mhorimoto/k2503100/DOCS/DOC190227-20190227140005.pdf

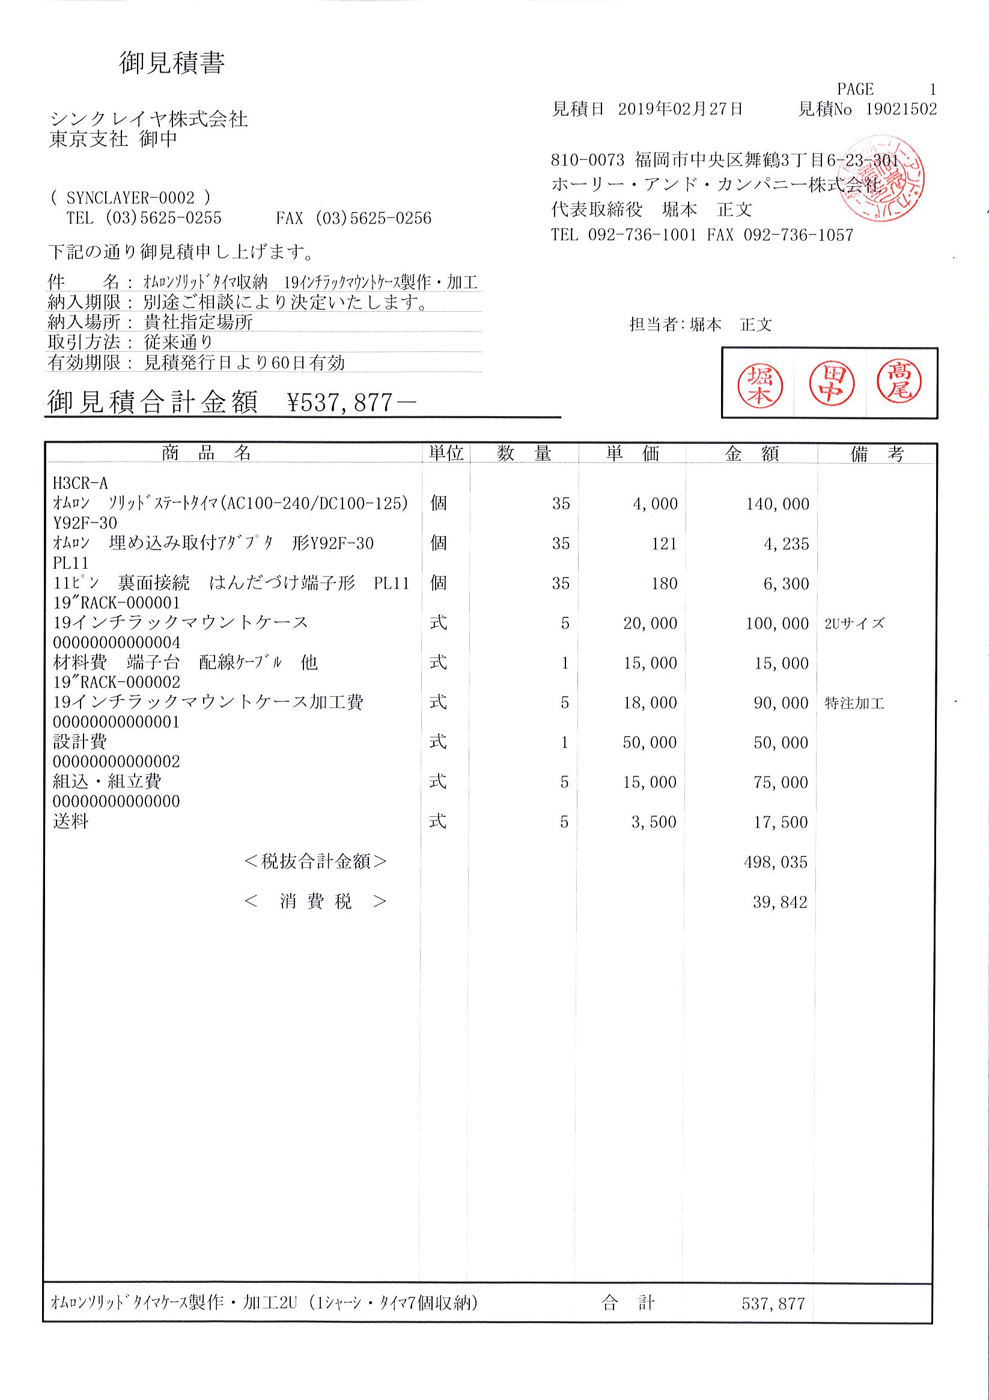
[picture p5: page 1]
