mhorimoto/k2503100/DOCS/image-sketch-1st.pdf

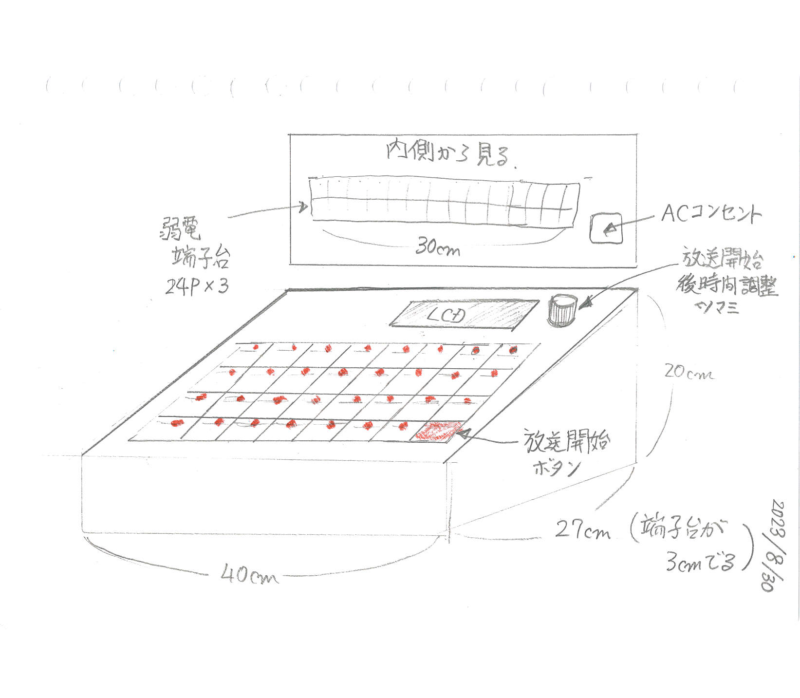
[picture p6: page 1]
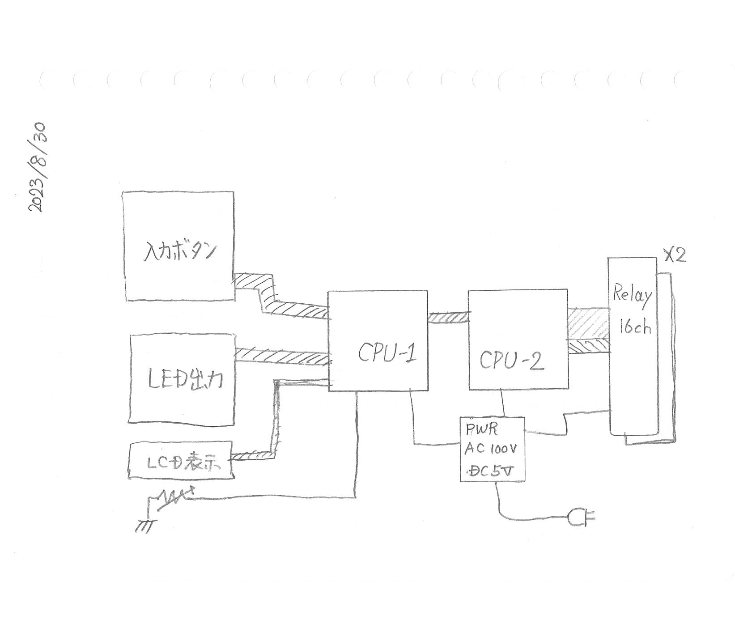
[picture p7: page 2]
