mhorimoto/k2503100/DOCS/workarea/Proforma  Invoice -PCBgogo20250206165503.pdf

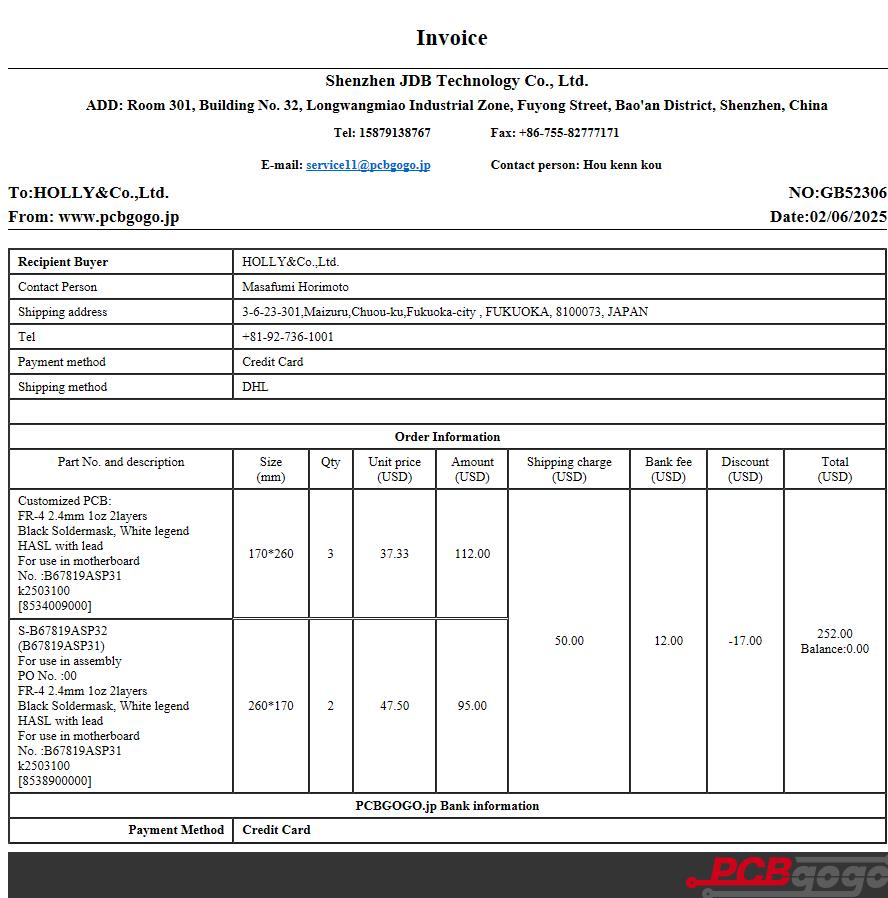
[picture p8: page 1]
