mhorimoto/k2503100/DOCS/workarea/20250203-case外観設計.pdf

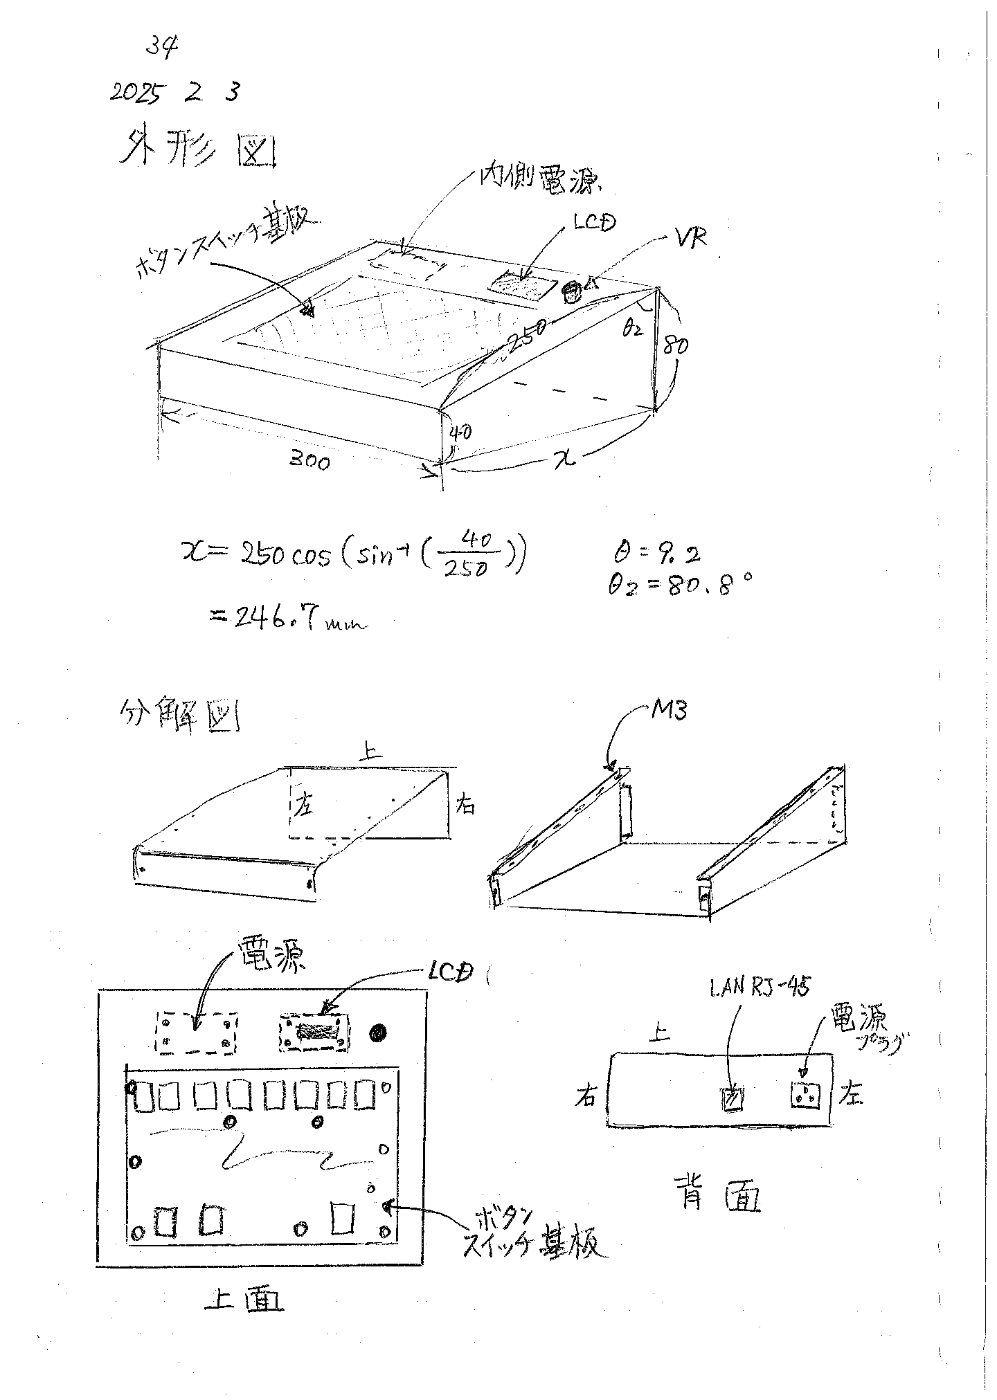
[picture p9: page 1]
