mhorimoto/k2503100/DOCS/workarea/PWR-LCD.pdf

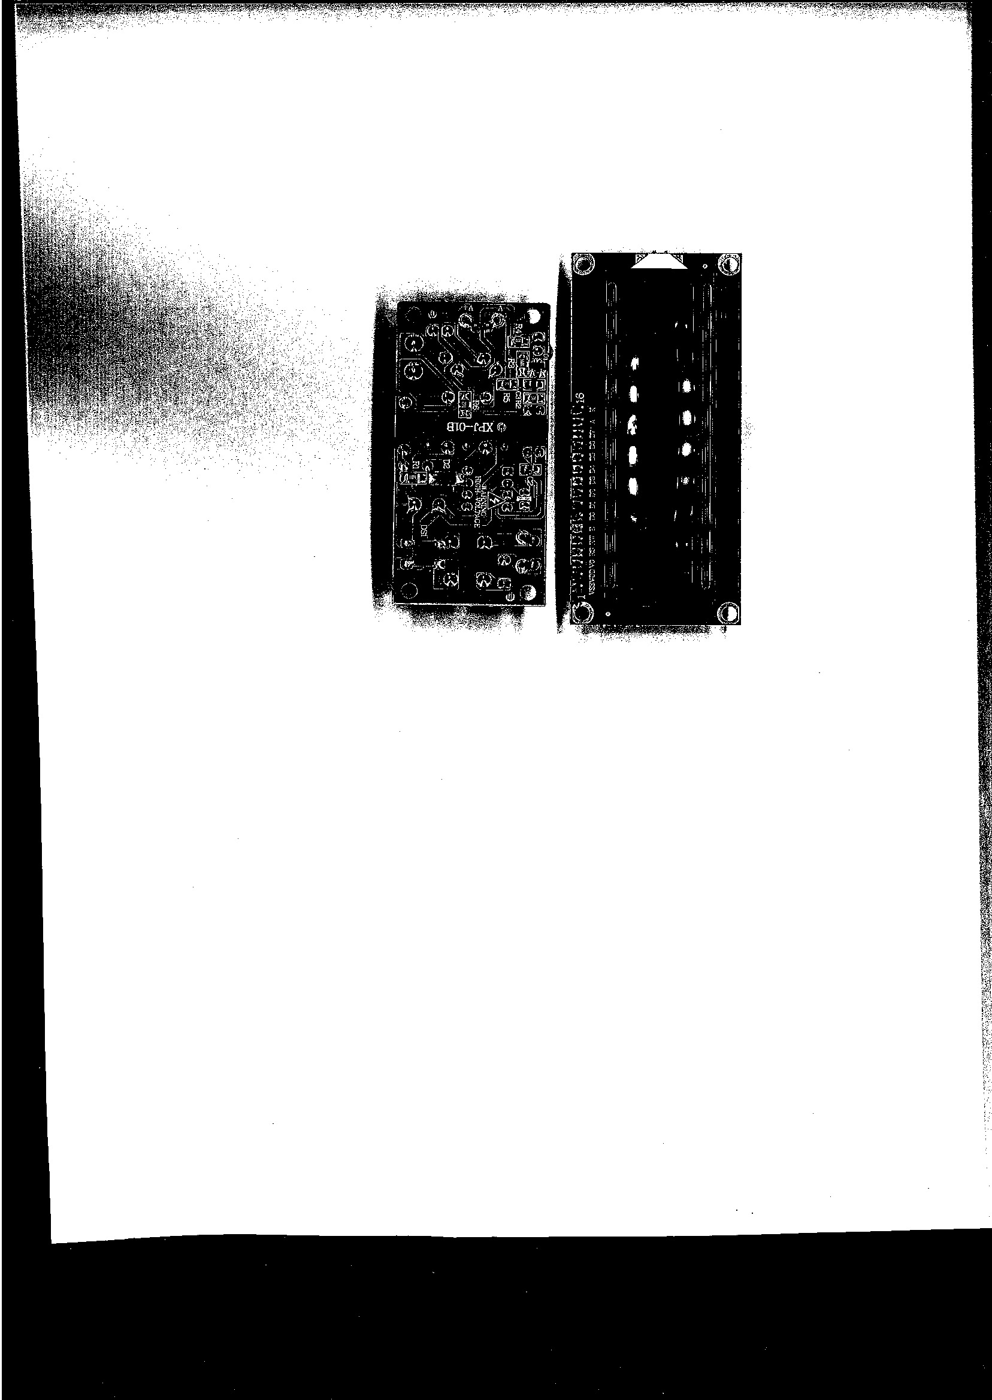
[picture p10: page 1]
