mhorimoto/k2503100/DOCS/workarea/S-B67819ASP32サンプル写真確認/2.jpg

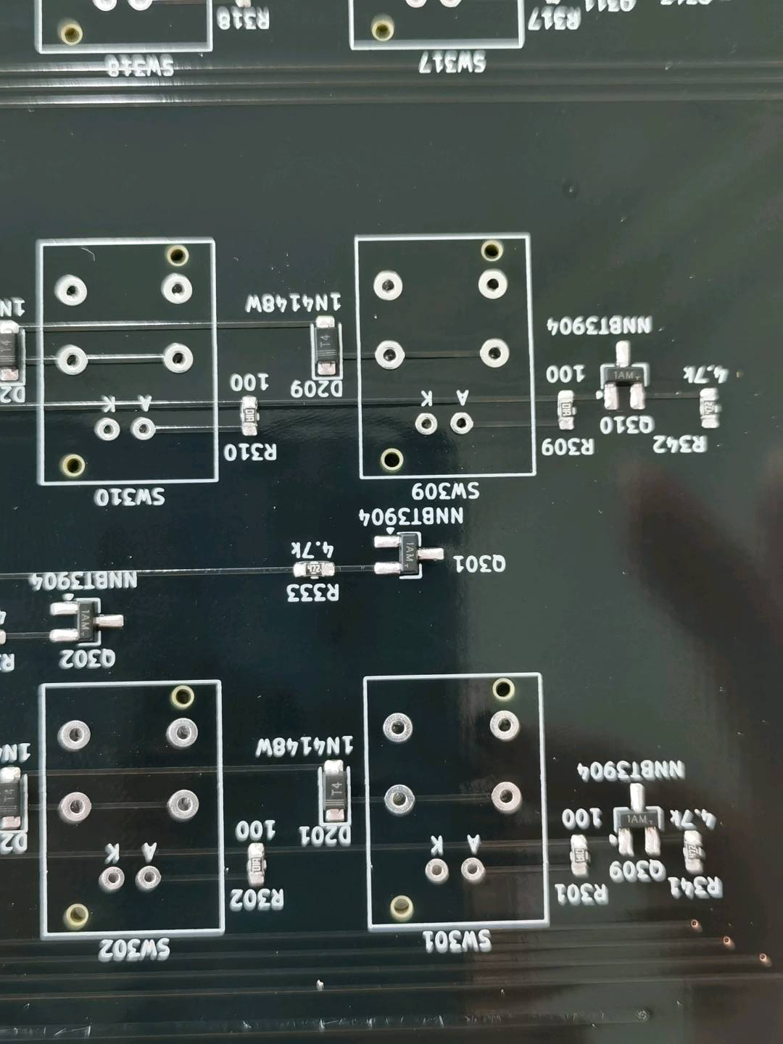
DOCS/workarea/S-B67819ASP32サンプル写真確認/2.jpg
