mhorimoto/k2503100/DOCS/image-sketch-2nd.pdf

## FM告知接点 (屋外のみ)

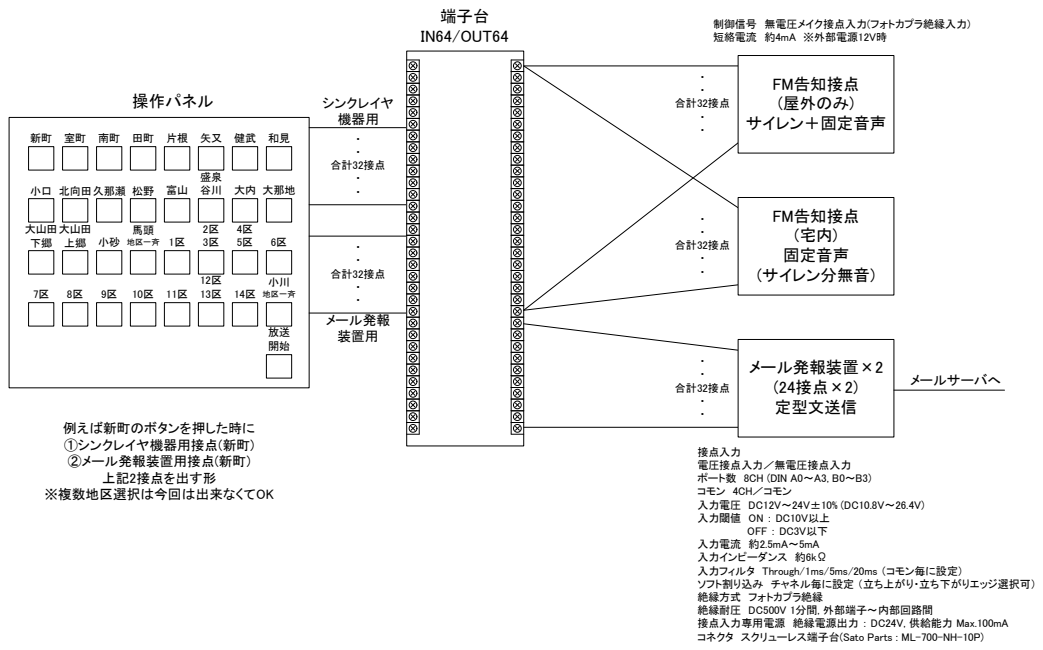
[picture p14: page 1]
サイレン＋固定音声; FM告知接点 (宅内) 固定音声 (サイレン分無音); メール発報装置×2 (24接点×2) 定型文送信; 操作パネル; シンクレイヤ; 機器用; メール発報 装置用; 端子台 IN64/OUT64; 大山田 下郷; 大山田; メールサーバへ; 地区一斉; OFF ： DC3V以下; 例えば新町のボタンを押した時に ①シンクレイヤ機器用接点(新町) ②メール発報装置用接点(新町) 上記2接点を出す形 ※複数地区選択は今回は出来なくてOK

制御信号　無電圧メイク接点入力(フォトカプラ絶縁入力)
短絡電流　約4mA　※外部電源12V時

谷川 大内 大那地

小口 北向田久那瀬 松野 富山

接点入力
電圧接点入力／無電圧接点入力
ポート数　8CH (DIN A0～A3, B0～B3)
コモン　4CH／コモン
入力電圧　DC12V～24V±10% (DC10.8V～26.4V)
入力閾値　ON ： DC10V以上
入力電流　約2.5mA～5mA
入力インピーダンス　約6kΩ
入力フィルタ　Through/1ms/5ms/20ms （コモン毎に設定）
ソフト割り込み　チャネル毎に設定 （立ち上がり・立ち下がりエッジ選択可）
絶縁方式　フォトカプラ絶縁
絶縁耐圧　DC500V 1分間, 外部端子～内部回路間
接点入力専用電源　絶縁電源出力 ： DC24V, 供給能力 Max.100mA
コネクタ　スクリューレス端子台(Sato Parts : ML-700-NH-10P)
