mhorimoto/k2503100/KiCAD/schema.pdf

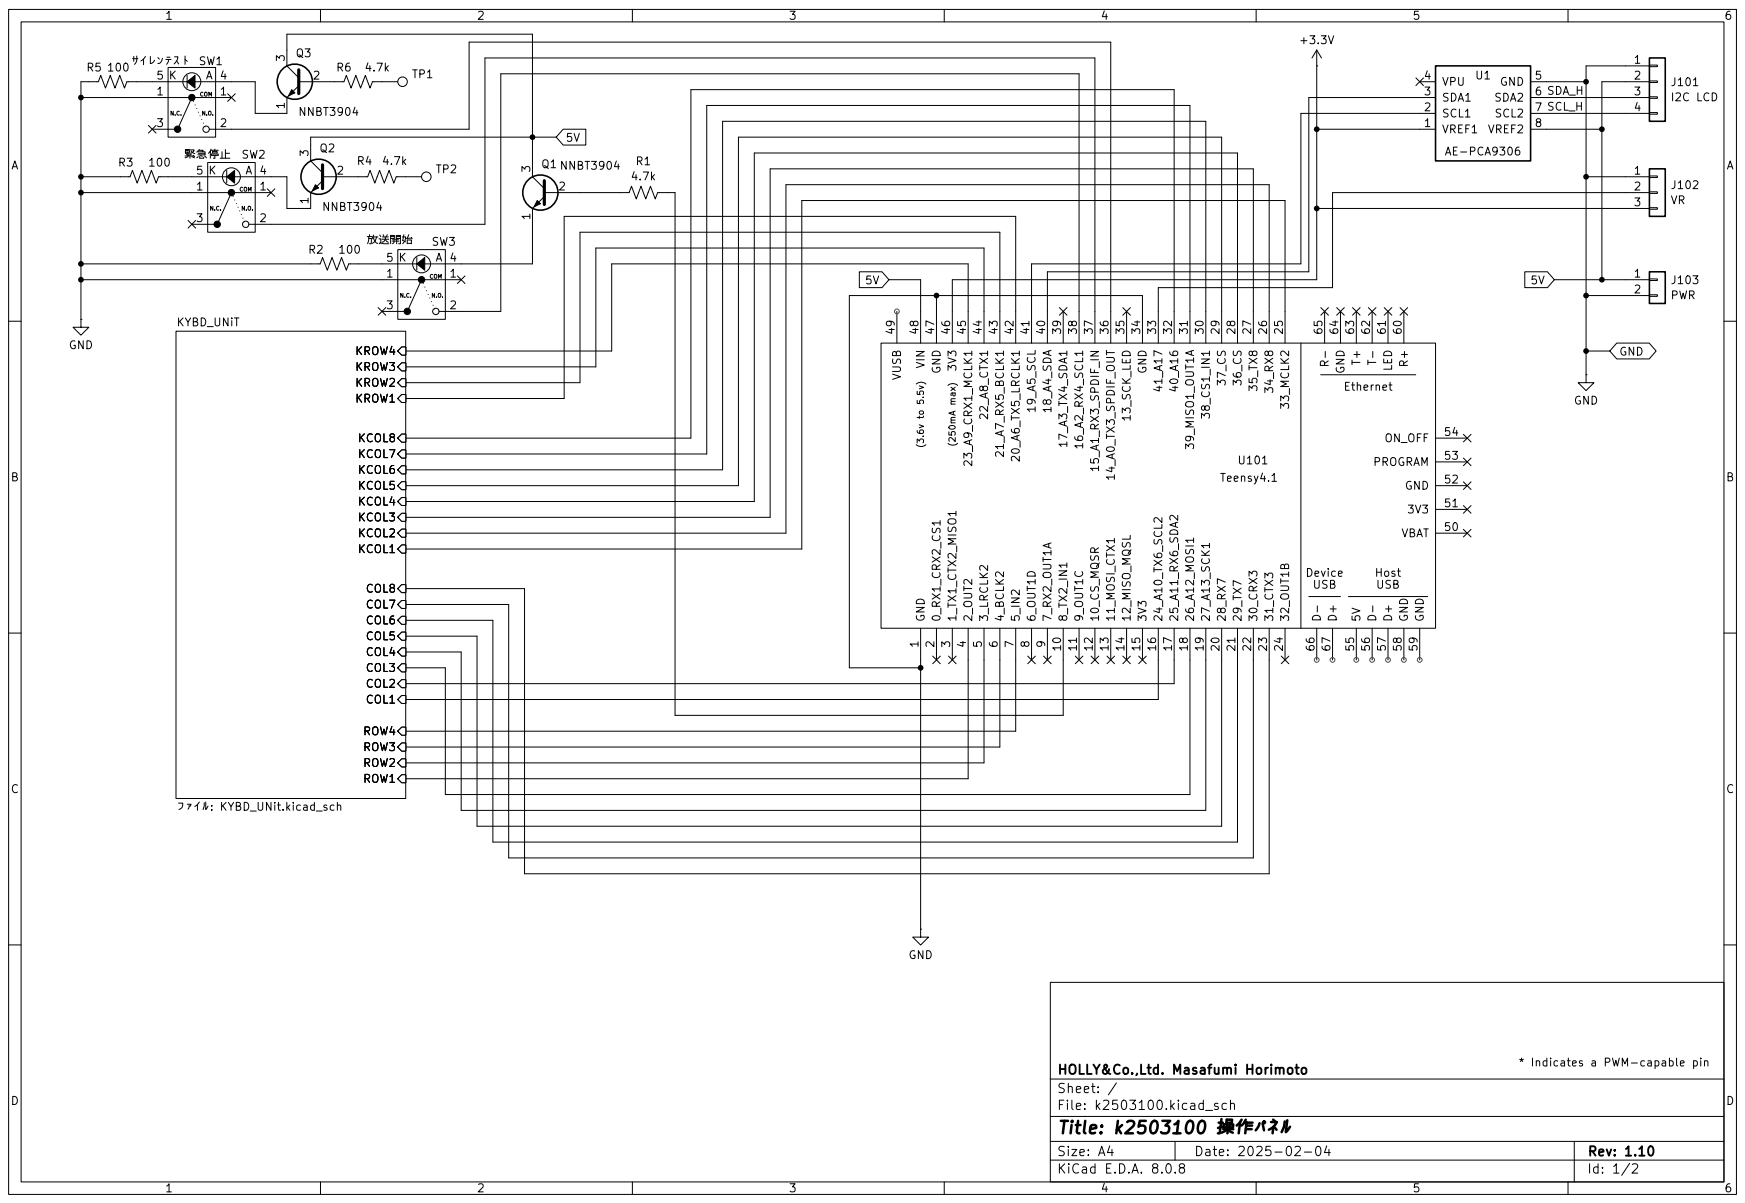
[picture p21: page 1]

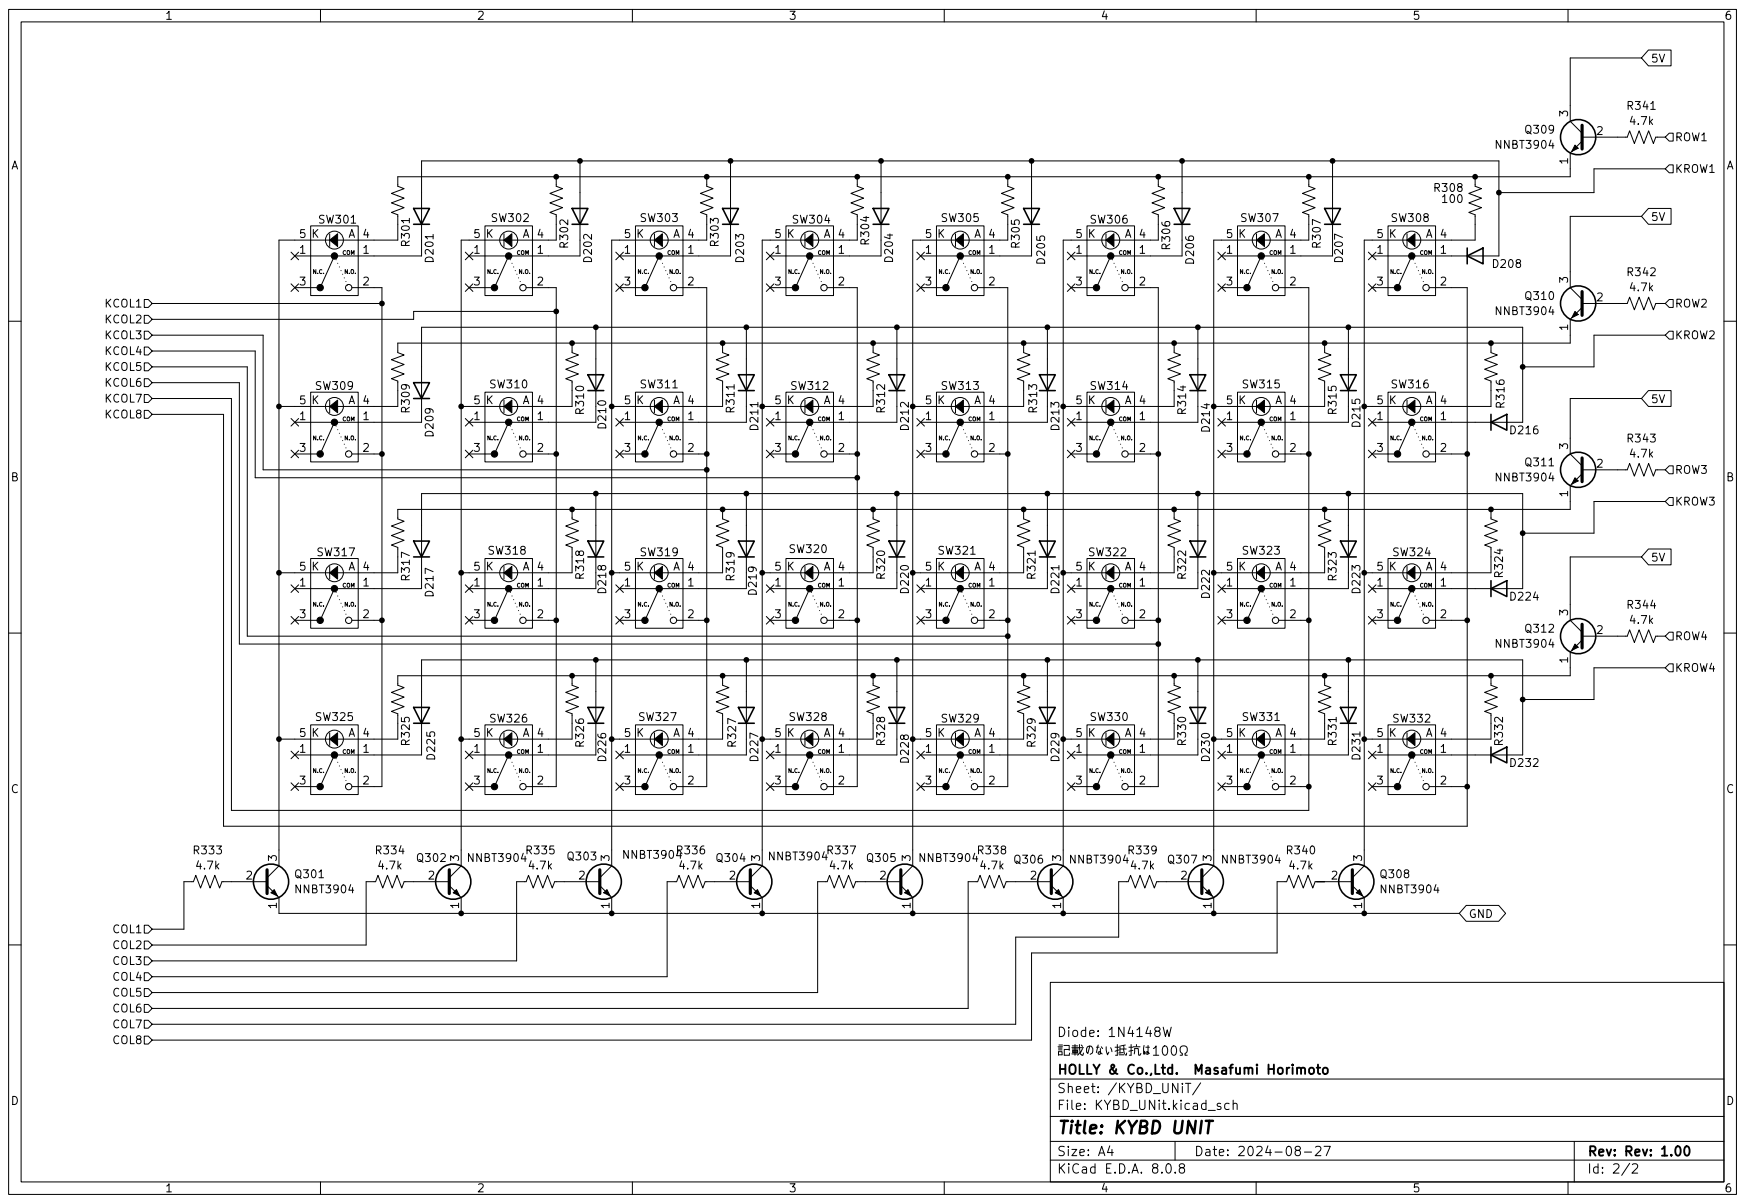
[picture p22: page 2]
