mhorimoto/k2503100/KiCAD/case1.pdf

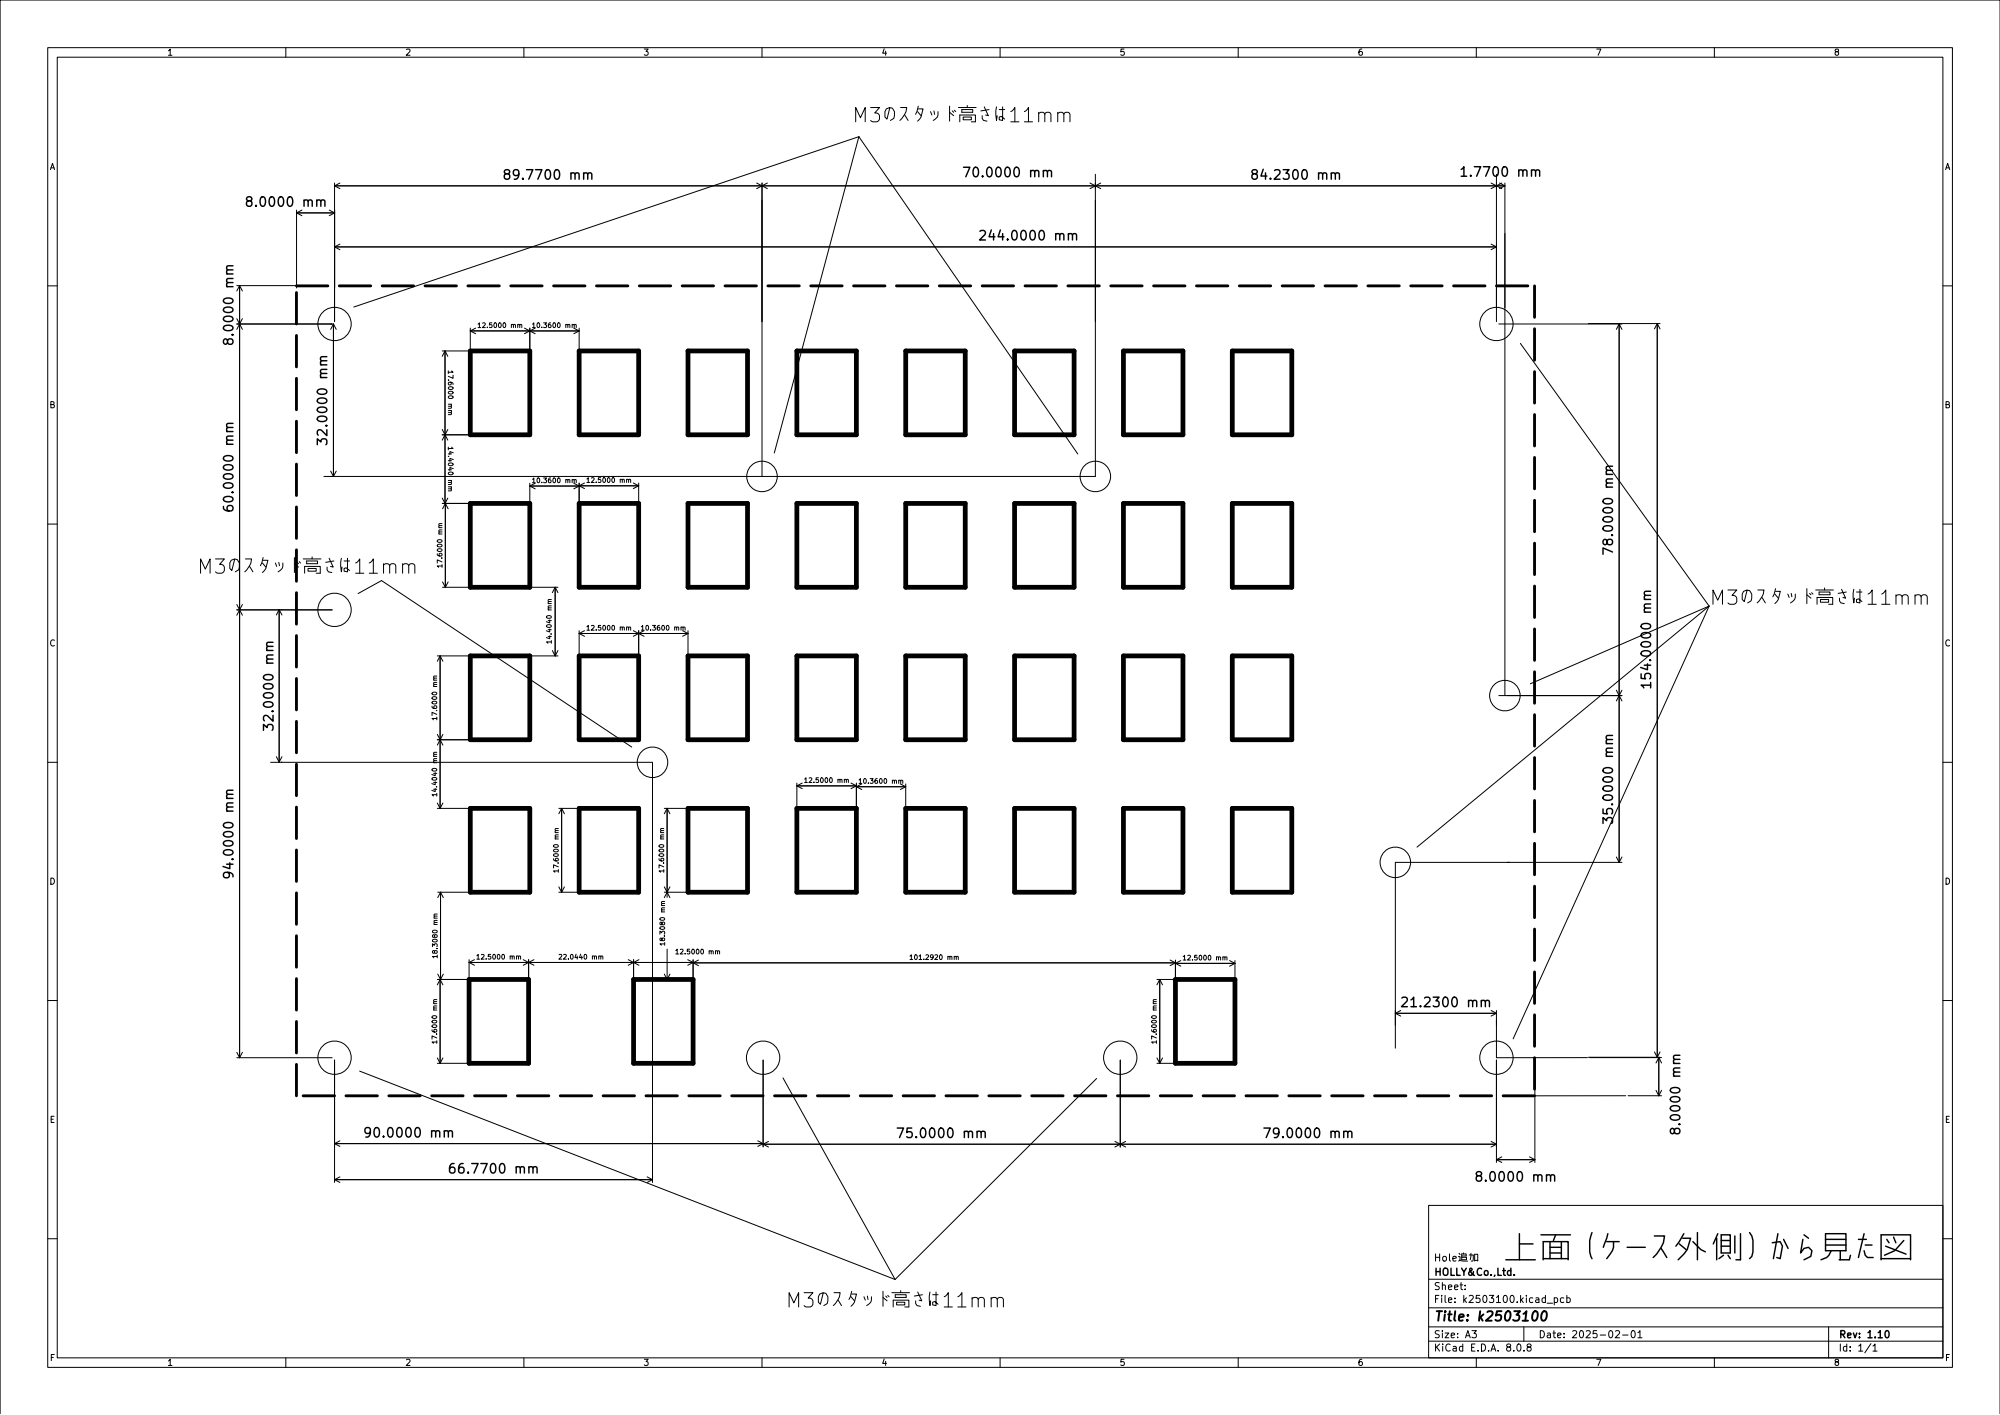
[picture p23: page 1]
