mhorimoto/k2503100/DOCS/workarea/W21888A0000.pdf

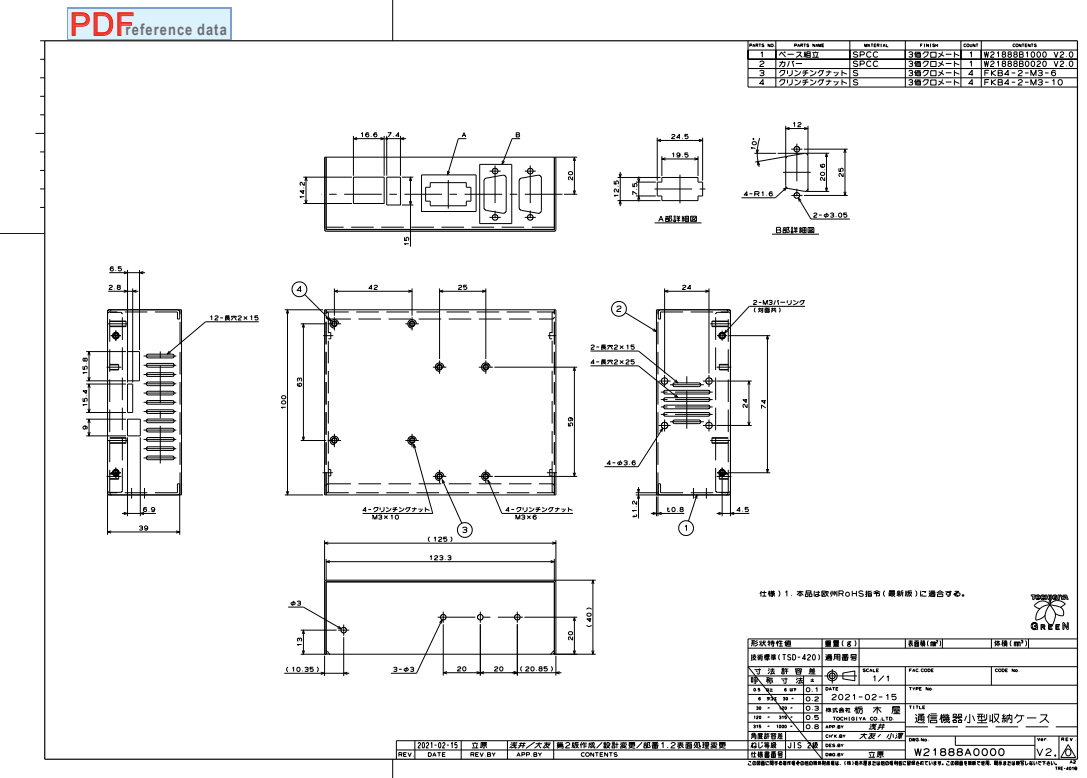
[picture p24: page 1]
PDFreference data
