mhorimoto/k2503100/DOCS/workarea/W21935A0000.pdf

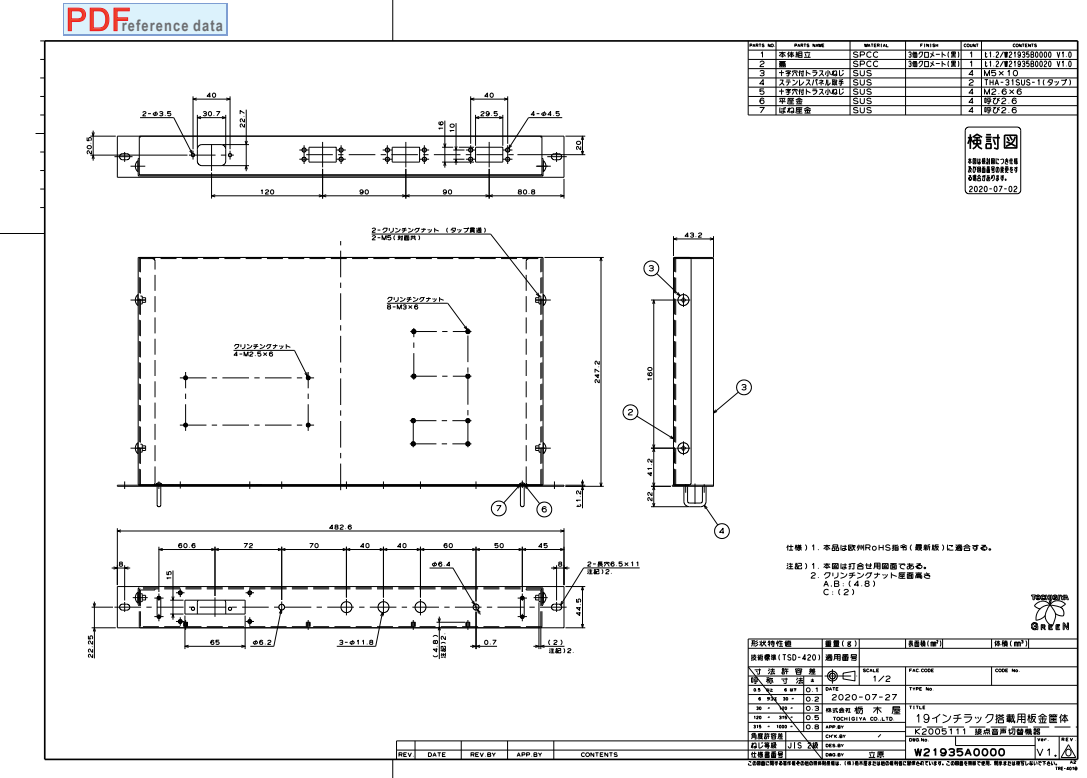
[picture p25: page 1]
PDFreference data

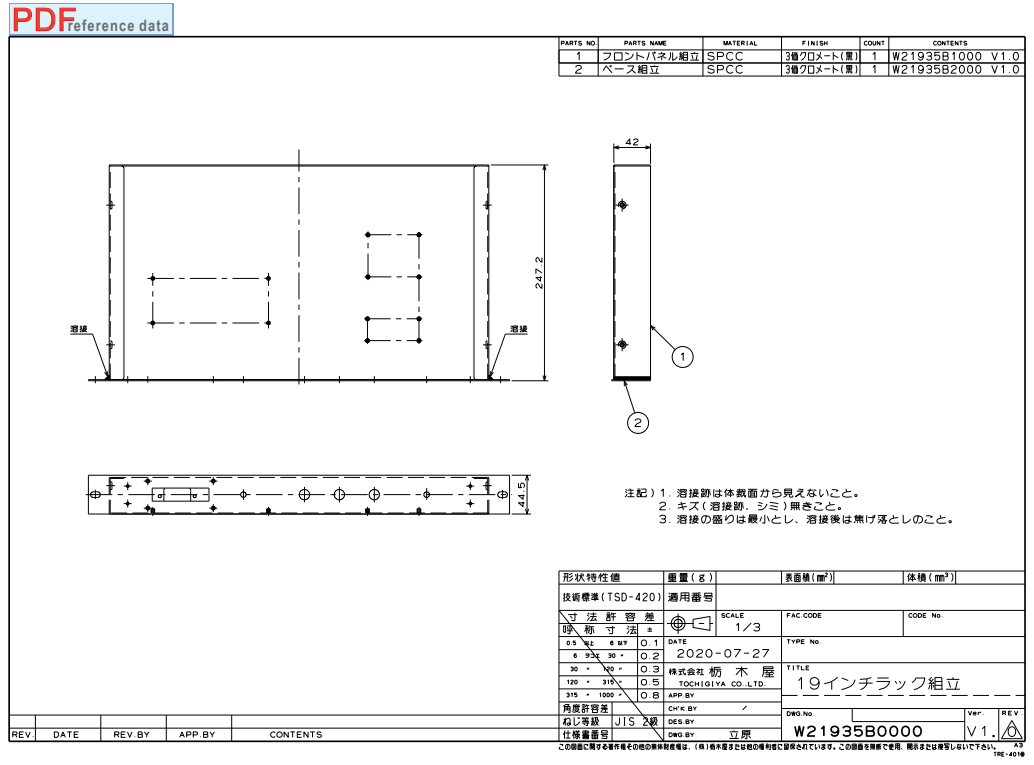
[picture p26: page 2]

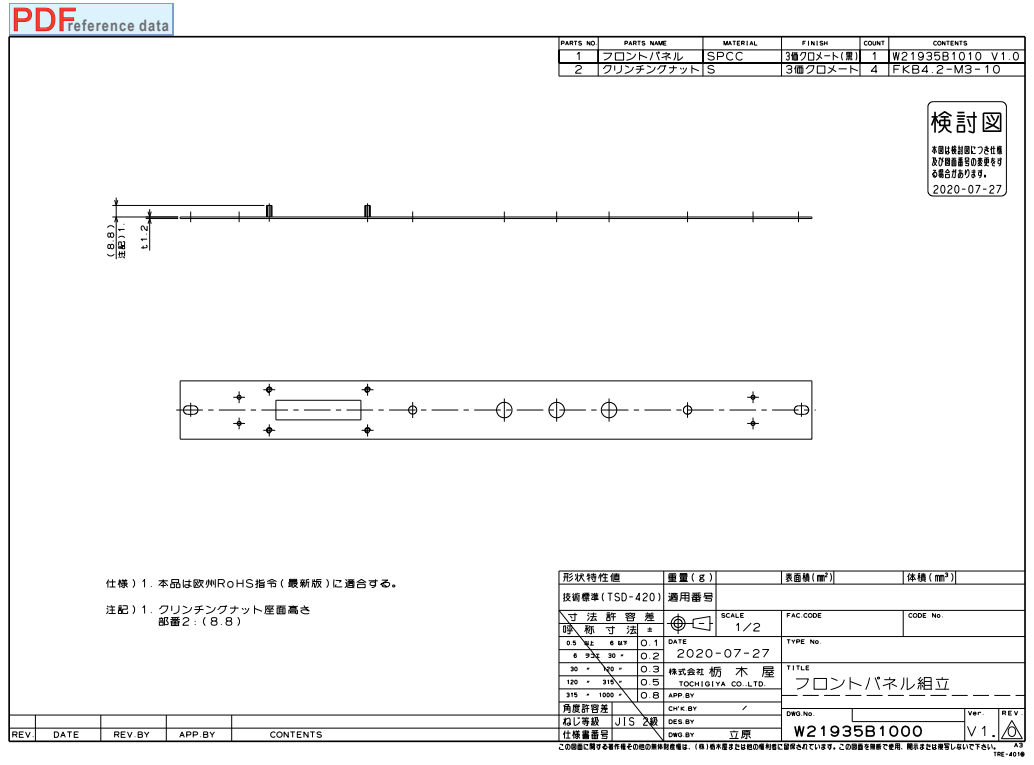
[picture p27: page 3]

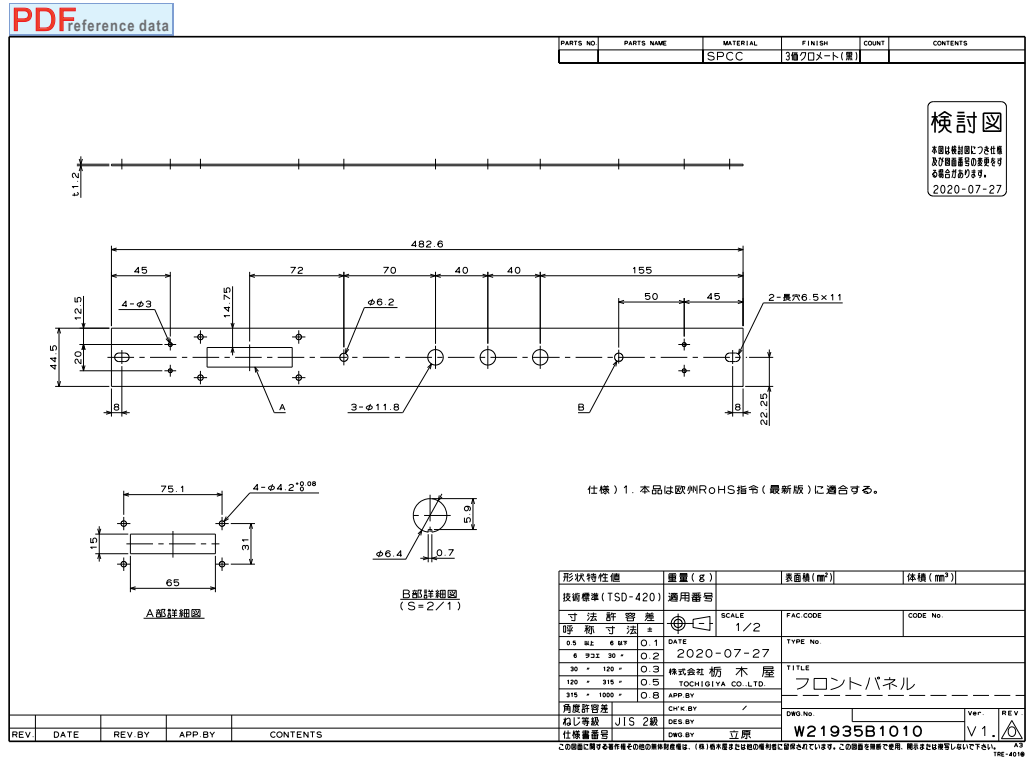
[picture p28: page 4]

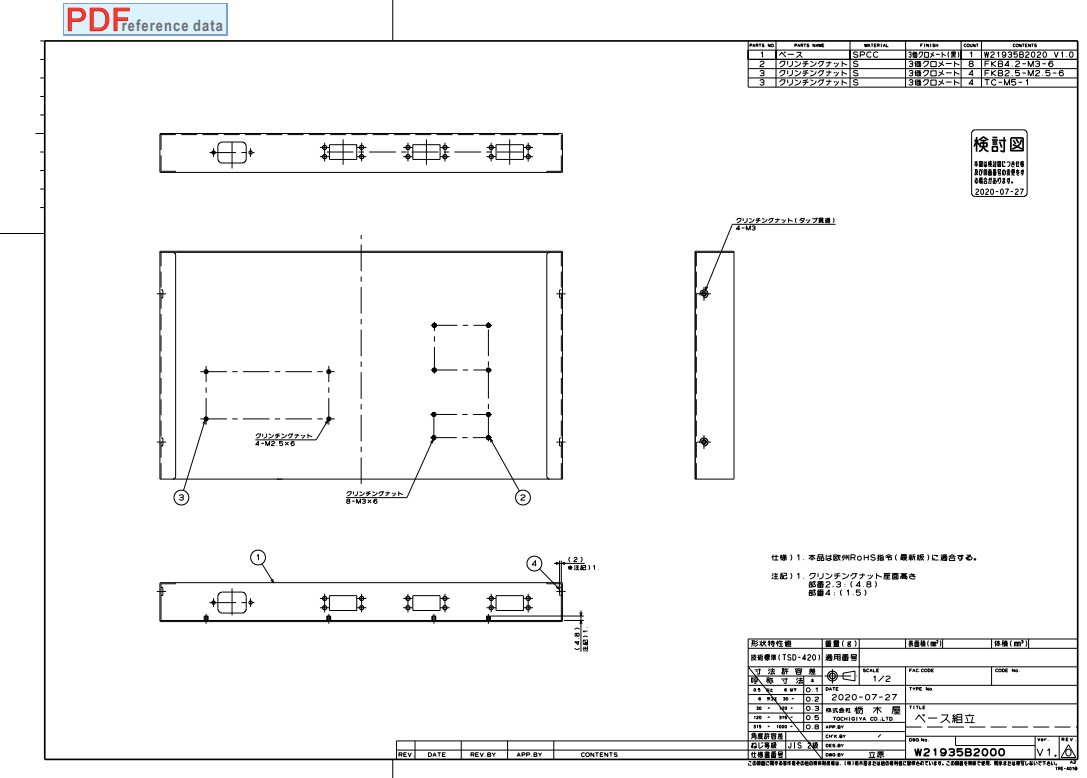
[picture p29: page 5]

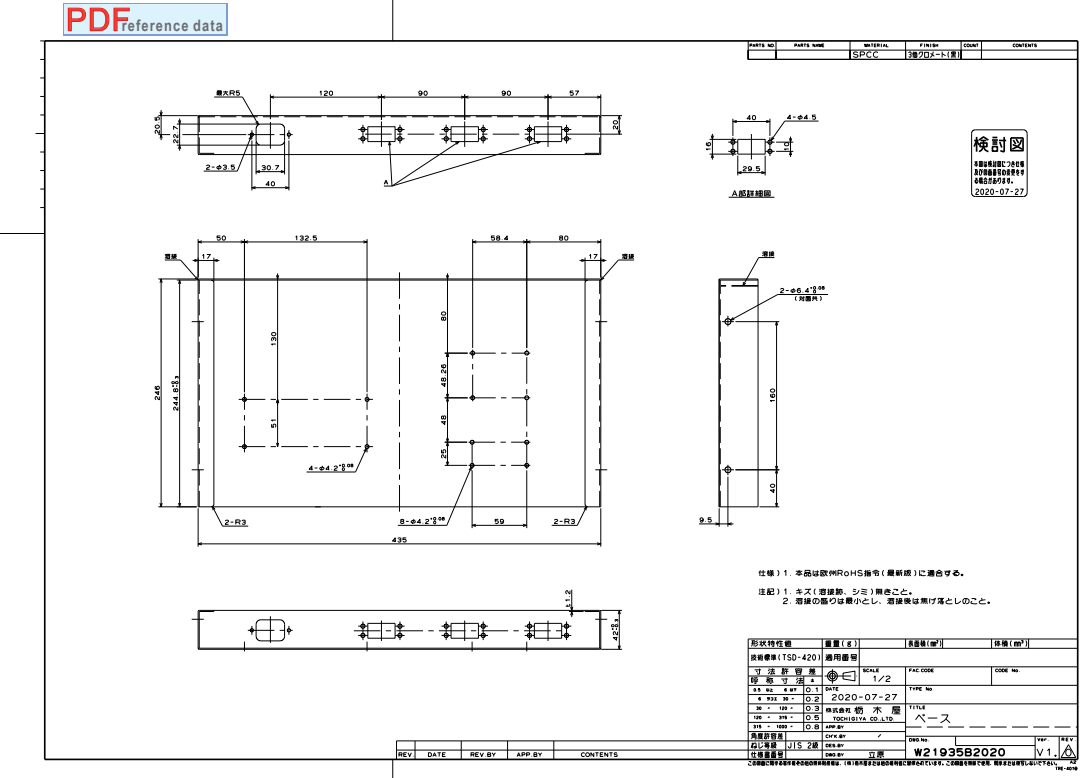
[picture p30: page 6]

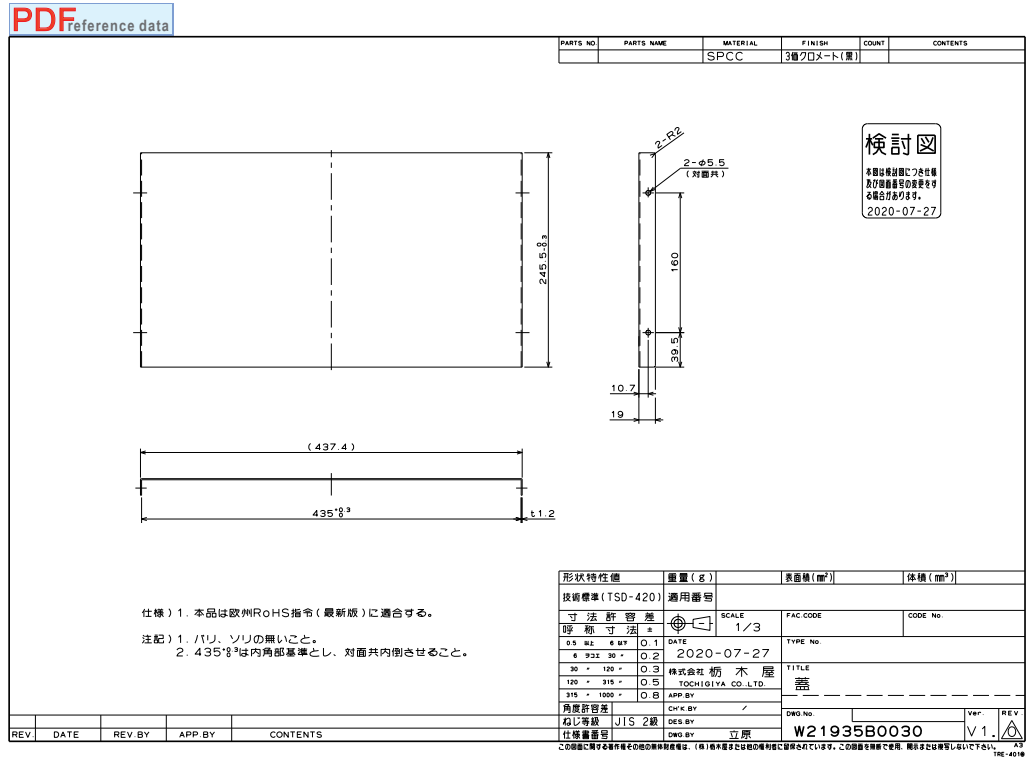
[picture p31: page 7]
