mhorimoto/k2503100/DOCS/workarea/DIAGRAM02.pdf

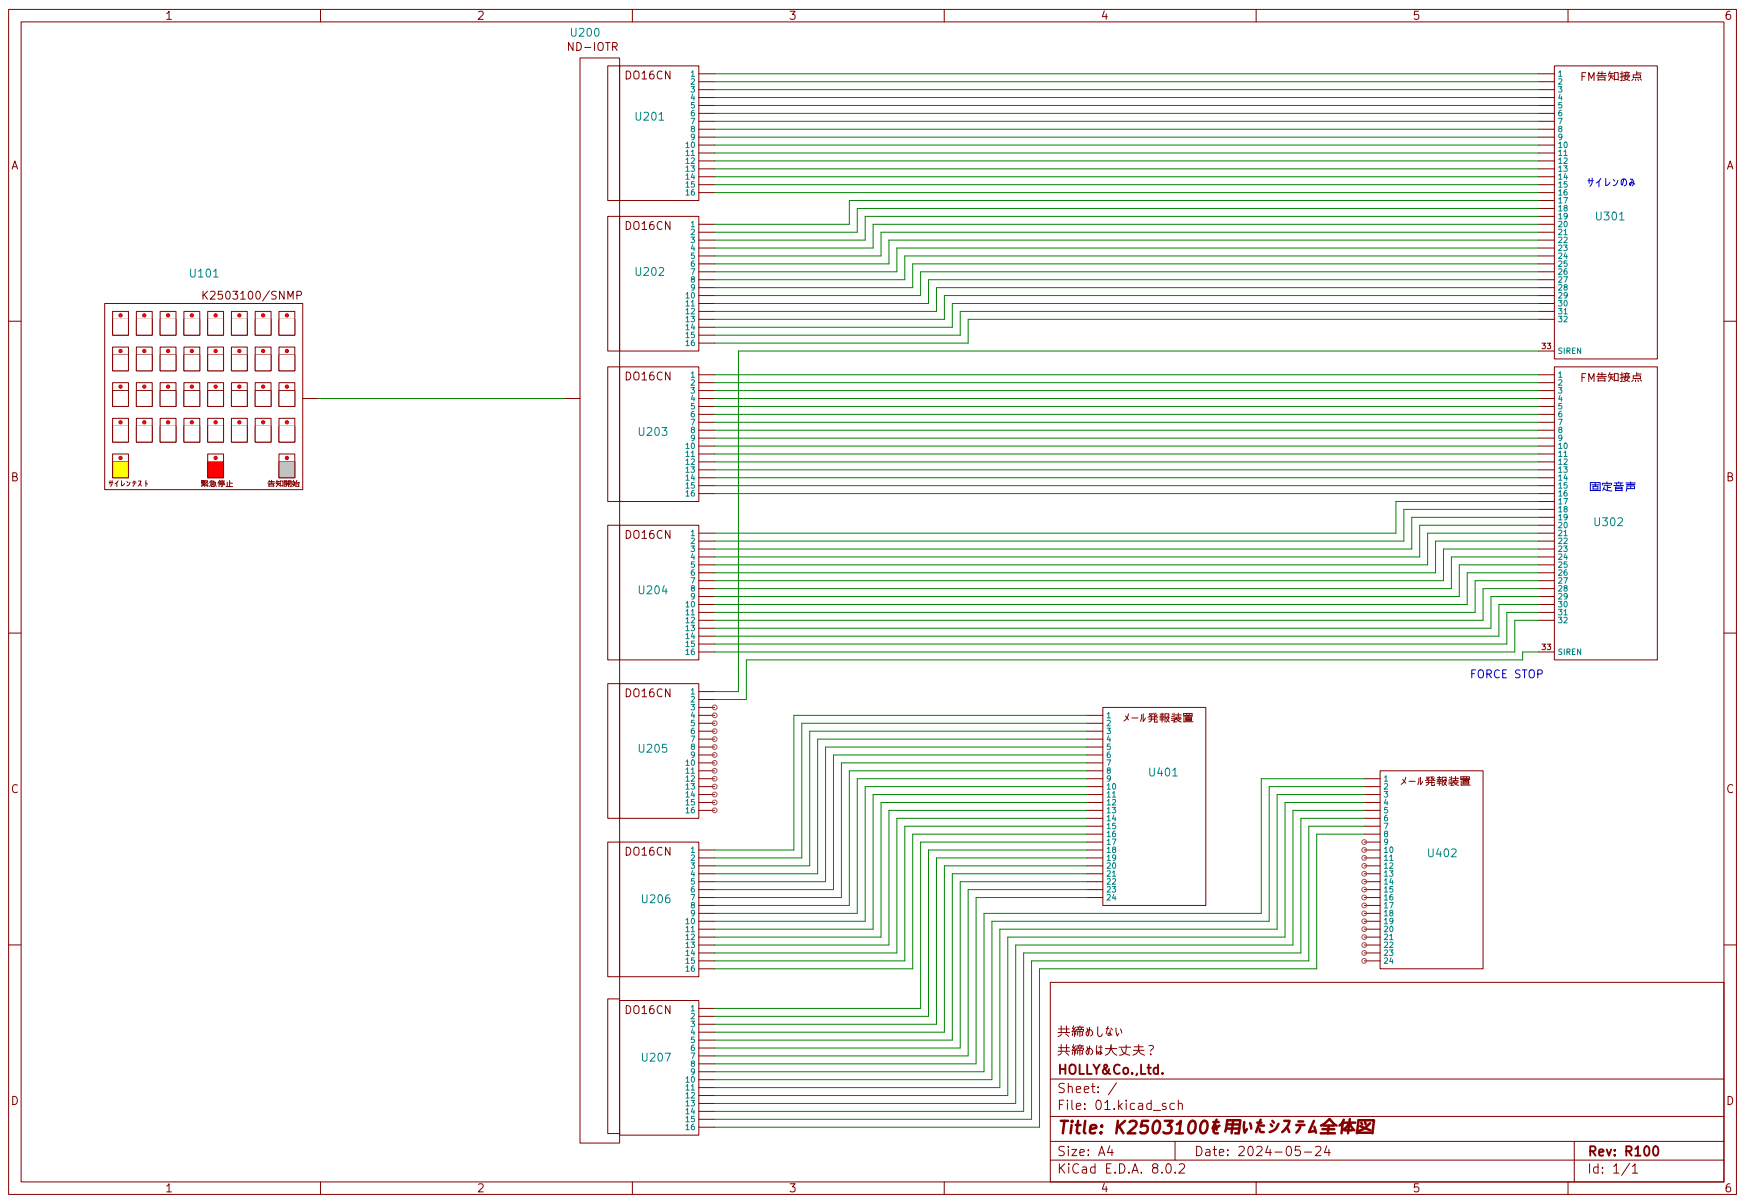
[picture p32: page 1]
