mhorimoto/k2503100/DOCS/workarea/DIAGRAM01.pdf

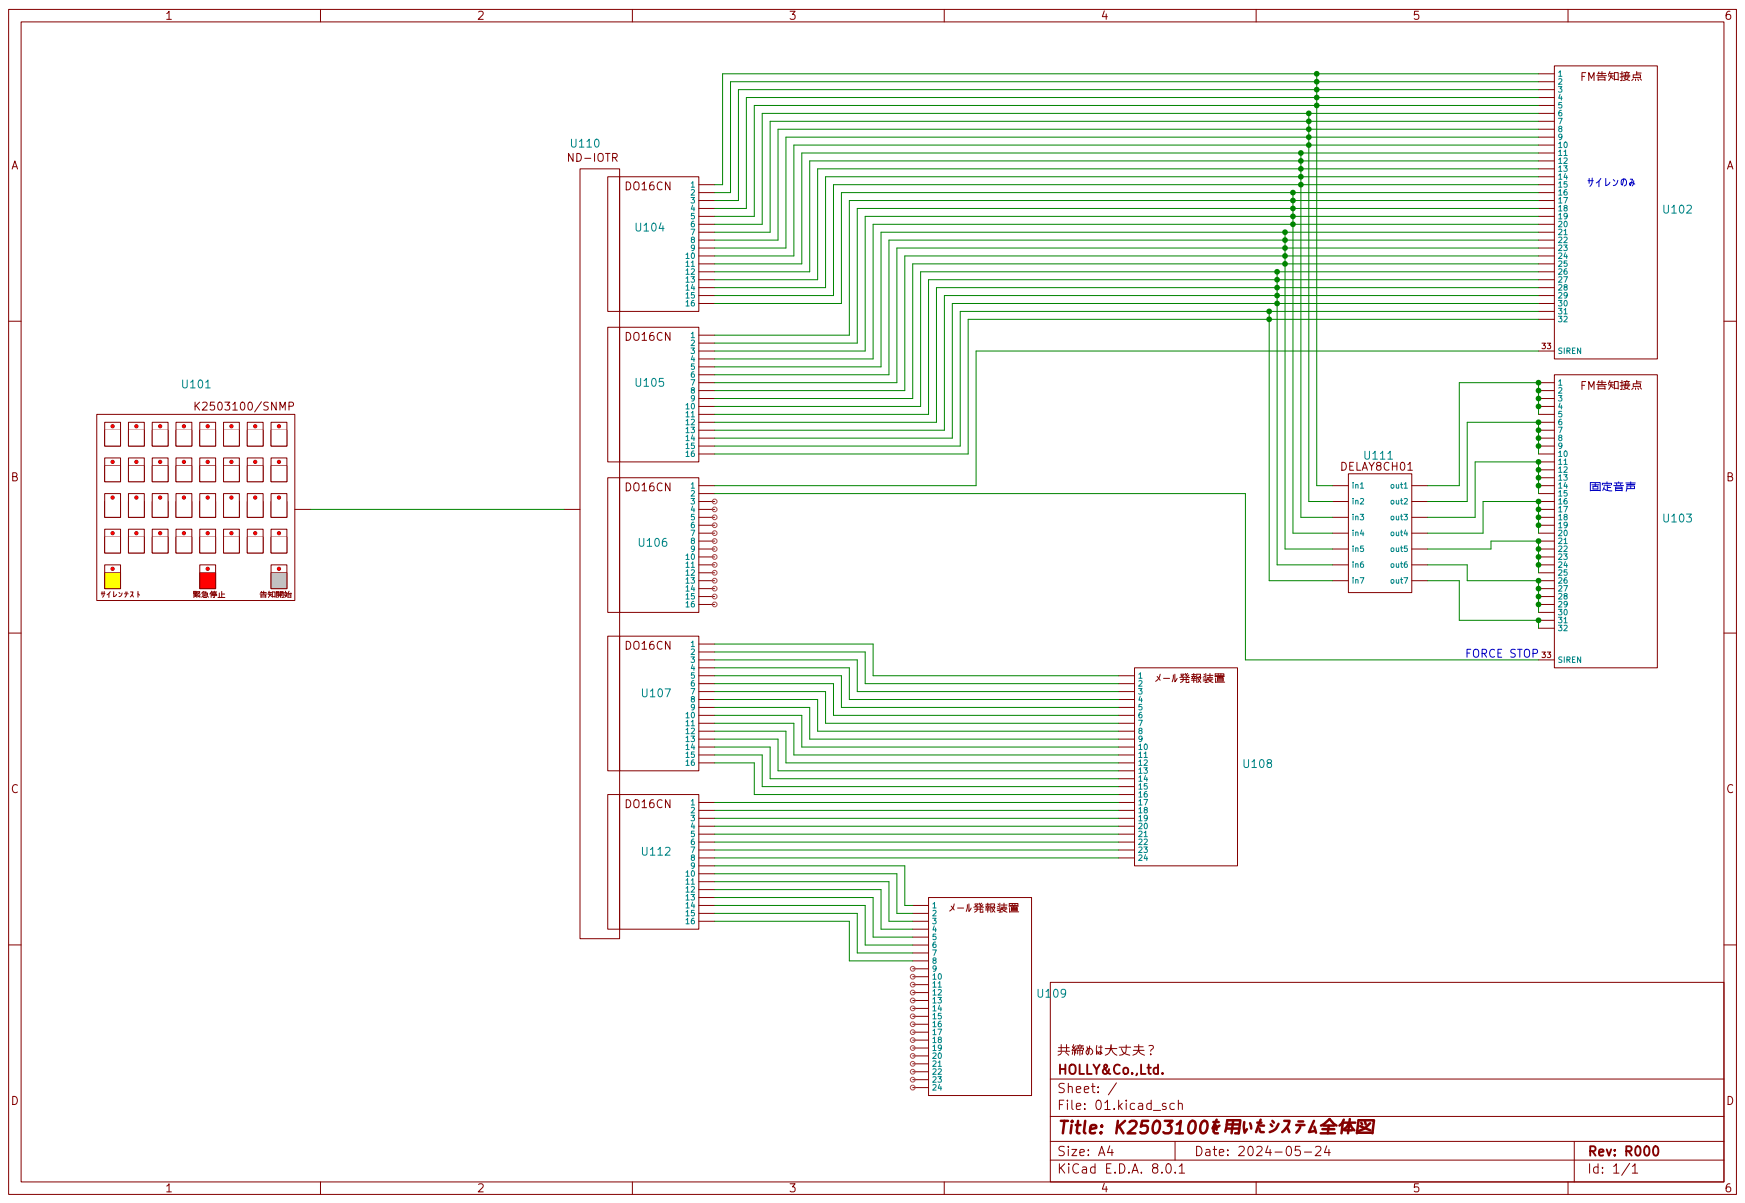
[picture p33: page 1]
